StefyAlex24/WorkExperienceProject_8x8LEDMATRIX/LEDMatrix_abFace_Example01/Letter Refarance for LED Matrix.png

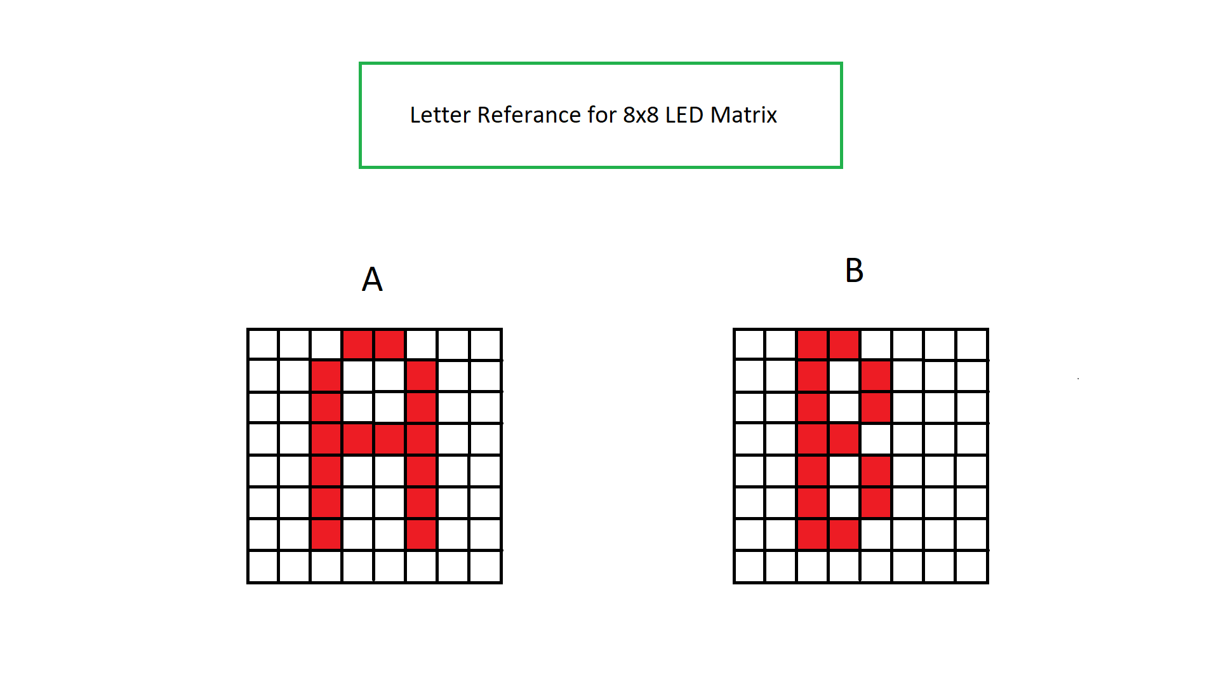
LEDMatrix_abFace_Example01/Letter Refarance for LED Matrix.png
